sierra-95/Max/images/electrical.jpg

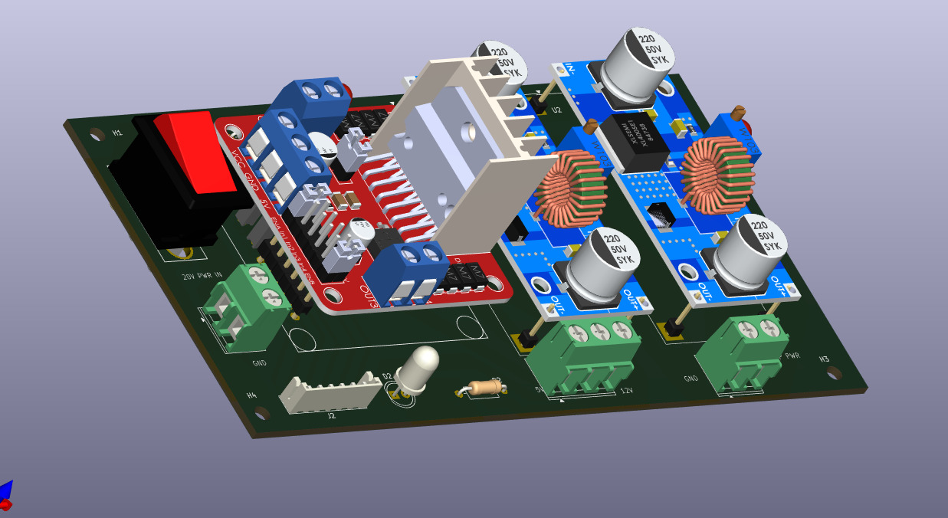
images/electrical.jpg
