sierra-95/Max/images/slam.jpeg

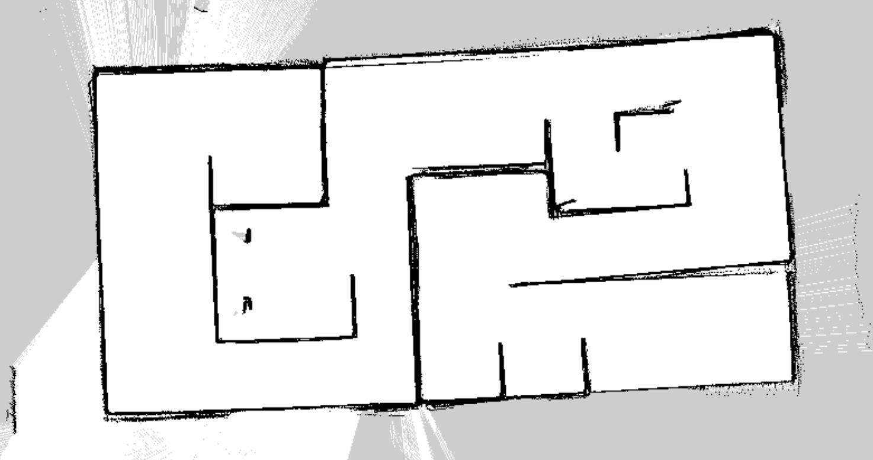
images/slam.jpeg
